DmytroY/ESP32-badge/images/server1.jpg

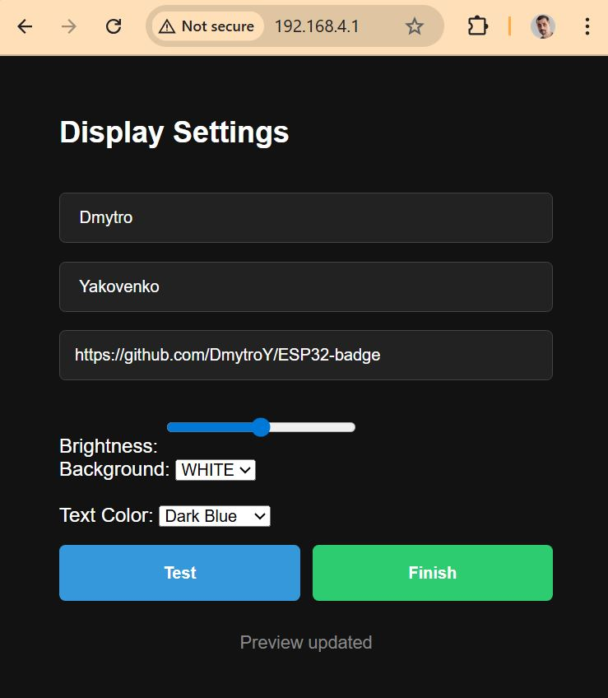
images/server1.jpg
